v5ma/neurotech/brainduino-server/assets/Postwarcity/textures/ivy-leaves.001_diffuse.png

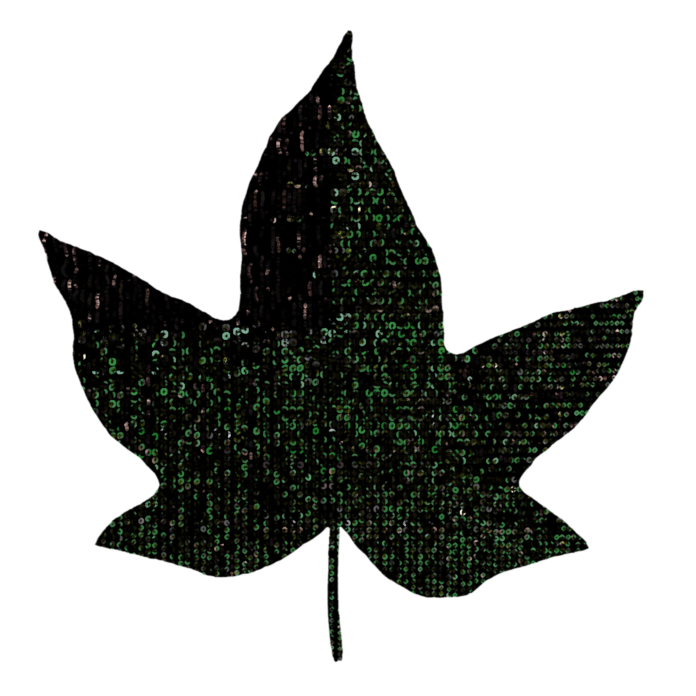
brainduino-server/assets/Postwarcity/textures/ivy-leaves.001_diffuse.png
