v5ma/neurotech/brainduino-server/assets/Postwarcity/textures/ivy-tronc.001_diffuse.png

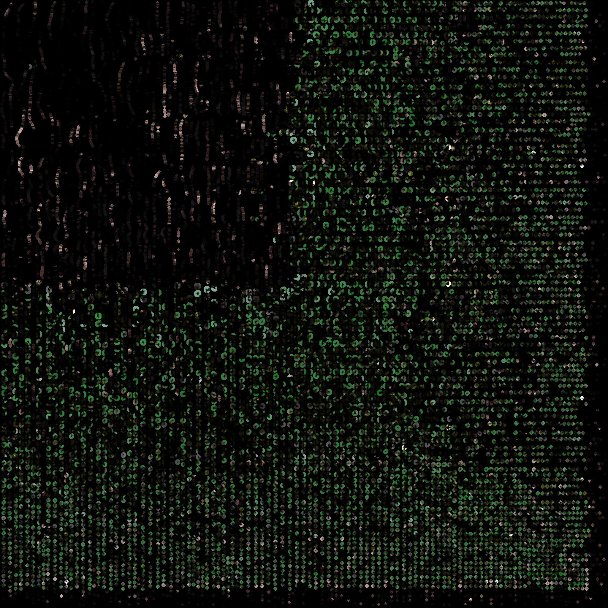
brainduino-server/assets/Postwarcity/textures/ivy-tronc.001_diffuse.png
