v5ma/neurotech/brainduino-server/assets/Postwarcity/textures/ivy-tronc_diffuse.png

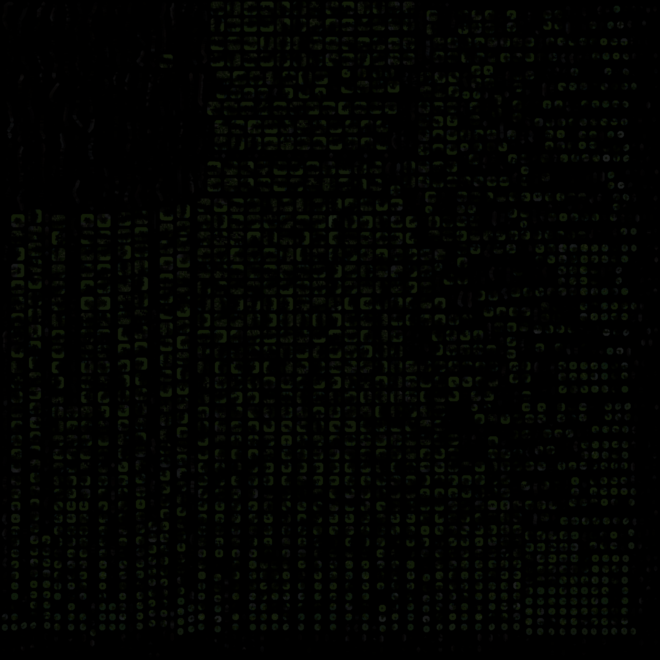
brainduino-server/assets/Postwarcity/textures/ivy-tronc_diffuse.png
