v5ma/neurotech/brainduino-server/assets/Postwarcity/textures/jante.001_normal.png

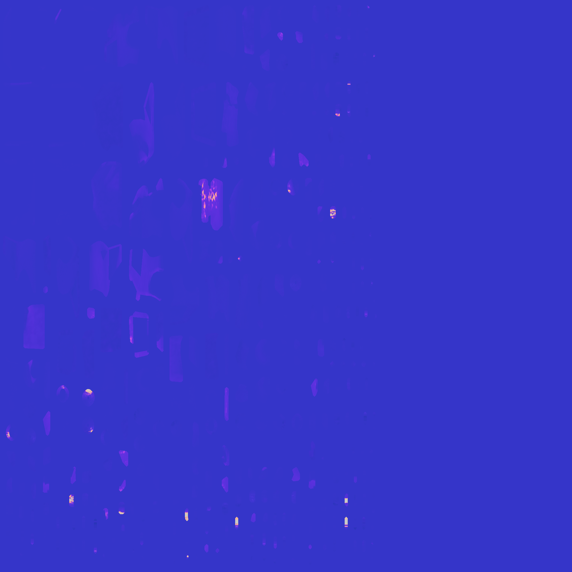
brainduino-server/assets/Postwarcity/textures/jante.001_normal.png
