v5ma/neurotech/brainduino-server/assets/Postwarcity/textures/TexturesCom_NaturePlants0038_1_alphamasked_S_emissive.png

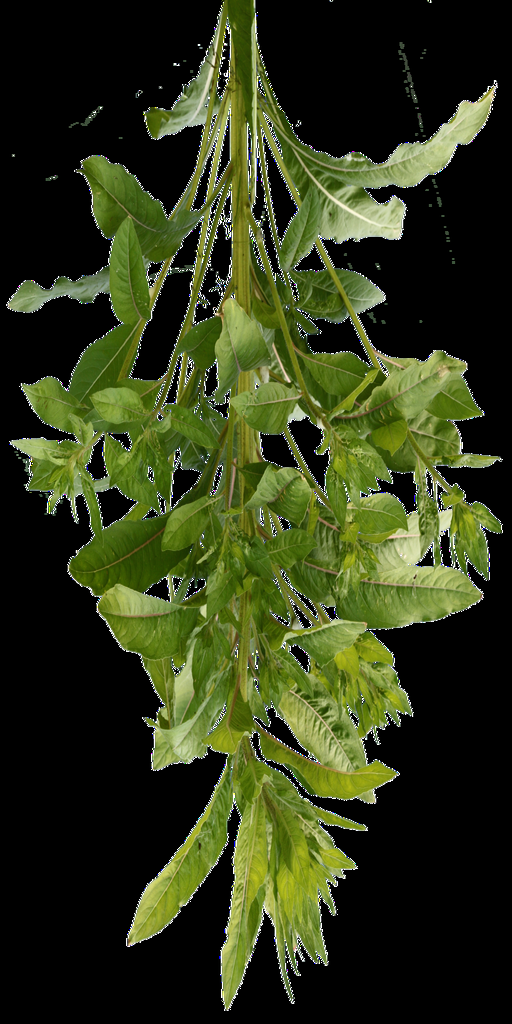
brainduino-server/assets/Postwarcity/textures/TexturesCom_NaturePlants0038_1_alphamasked_S_emissive.png
