v5ma/neurotech/brainduino-server/assets/Postwarcity/textures/TexturesCom_NaturePlants0052_1_alphamasked_S_diffuse.png

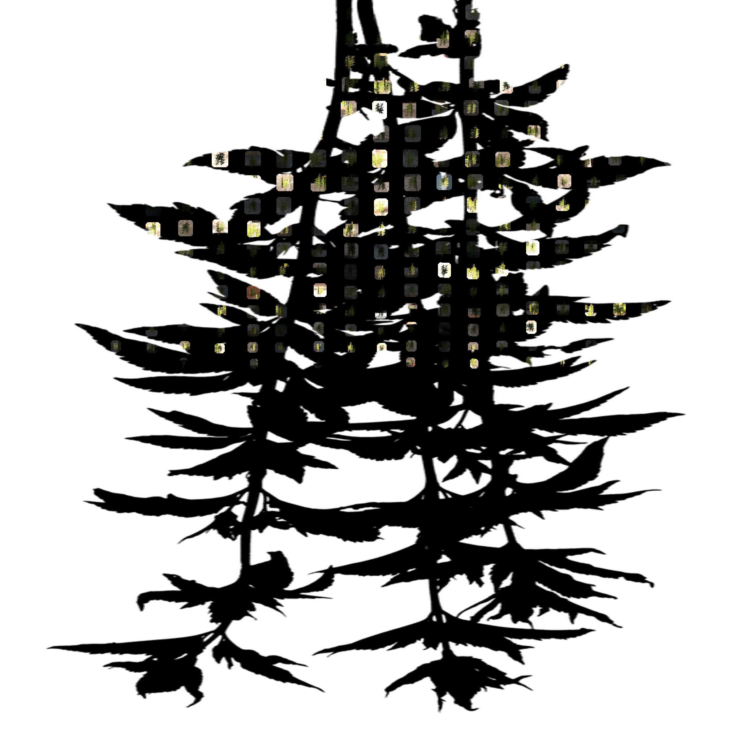
brainduino-server/assets/Postwarcity/textures/TexturesCom_NaturePlants0052_1_alphamasked_S_diffuse.png
