v5ma/neurotech/brainduino-server/assets/Postwarcity/textures/wall.002_diffuse.png

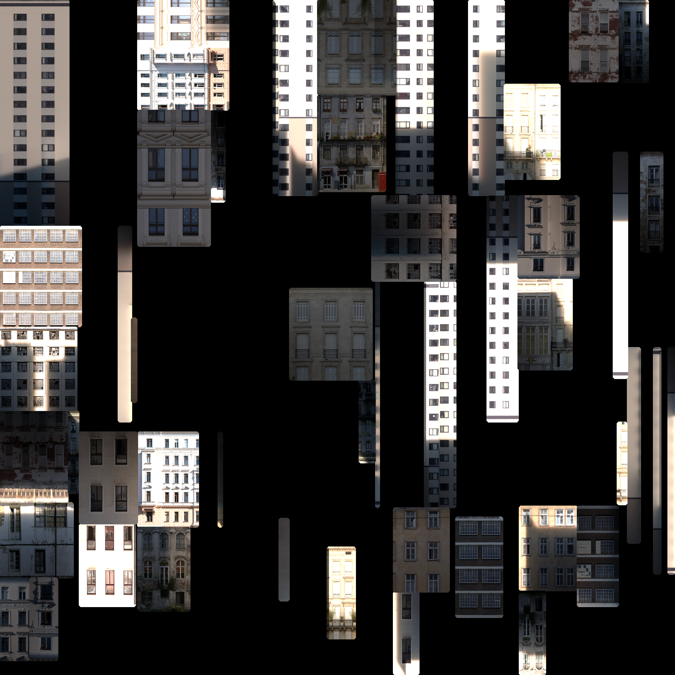
brainduino-server/assets/Postwarcity/textures/wall.002_diffuse.png
