v5ma/neurotech/brainduino-server/assets/Postwarcity/textures/wall_diffuse.png

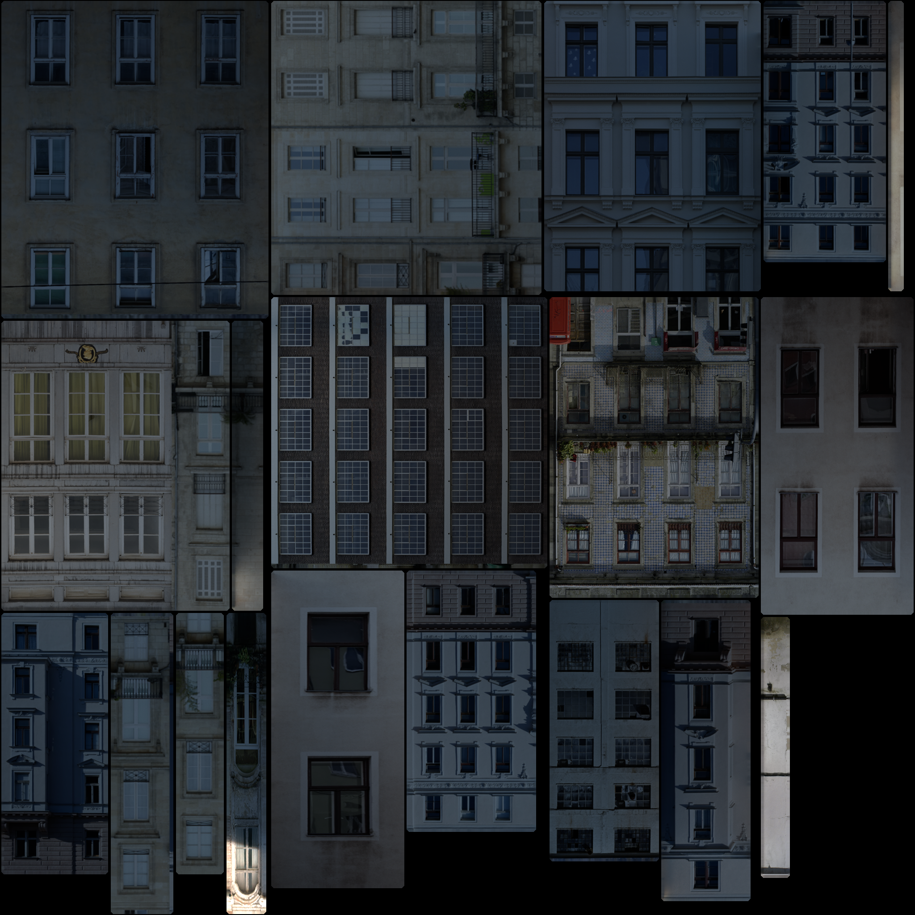
brainduino-server/assets/Postwarcity/textures/wall_diffuse.png
